Garfield-1314/Robot_Arm/CAD/3D模型文件/主视图.png

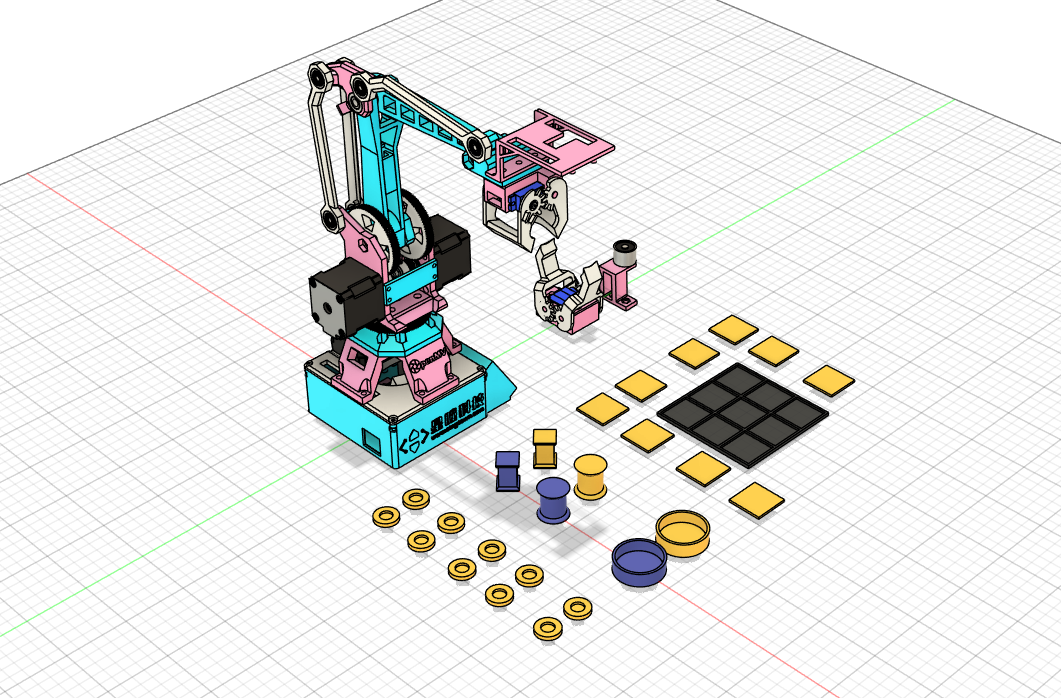
CAD/3D模型文件/主视图.png
